eoinest/blocked/enclosure/stl/fit-coupon.stl

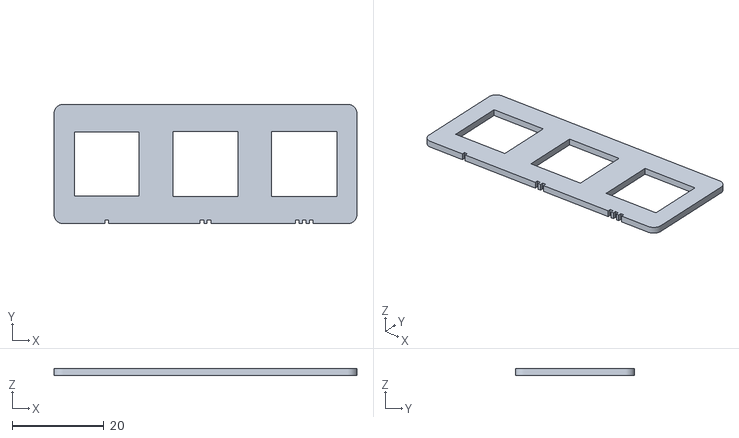
[picture p26: CAD file, 2026-09-06]
enclosure/stl/fit-coupon.stl
66.0 x 26.0 x 1.50
