eoinest/blocked/keycap/printed/stl/socket-fit-coupons.stl

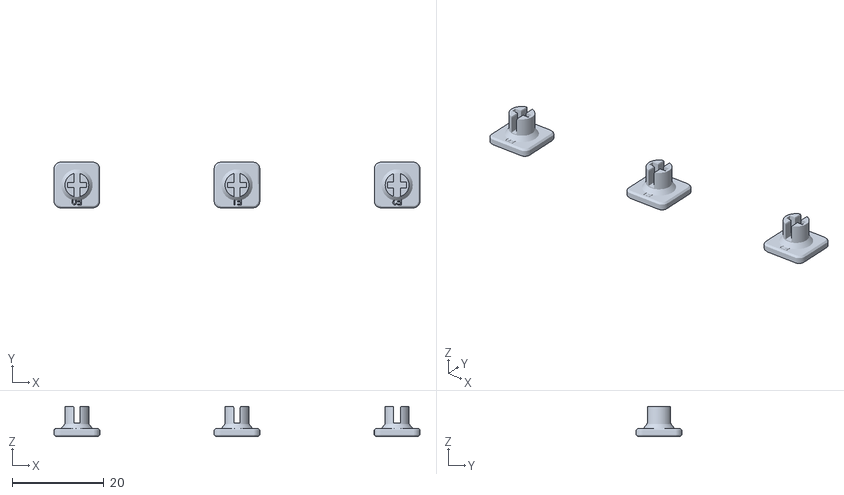
[picture p27: CAD file, 2026-09-07]
keycap/printed/stl/socket-fit-coupons.stl
80.0 x 10.0 x 6.60
